alustig3/unitron/pcb/labels/celsius.png

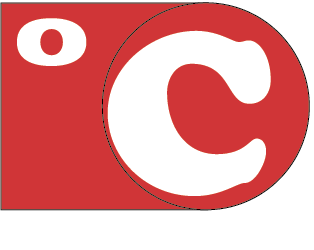
pcb/labels/celsius.png
