alustig3/unitron/pcb/labels/fahrenheit.png

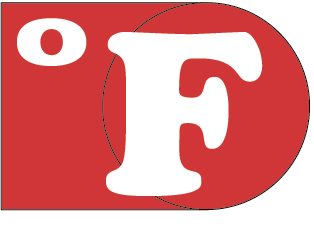
pcb/labels/fahrenheit.png
