alustig3/unitron/pcb/labels/feet.png

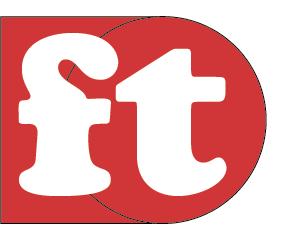
pcb/labels/feet.png
