alustig3/unitron/pcb/labels/meters.png

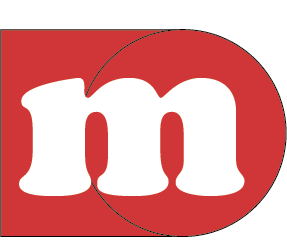
pcb/labels/meters.png
