alustig3/unitron/pcb/labels/miles.png

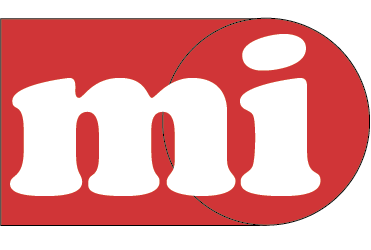
pcb/labels/miles.png
