alustig3/unitron/pcb/labels/millimeter.png

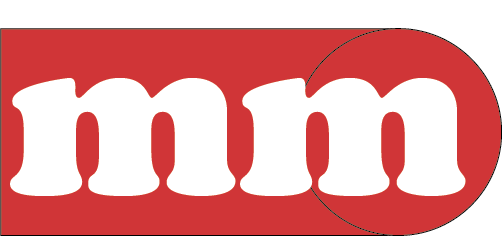
pcb/labels/millimeter.png
